trevidy/birthday-bot/all_frames.h

// Tổng hợp 772 frames - 128x64 pixels
// @khoi2mai
#ifndef ALL_FRAMES_H
#define ALL_FRAMES_H

#include "frames/frame_00000.h"
#include "frames/frame_00001.h"
#include "frames/frame_00002.h"
#include "frames/frame_00003.h"
#include "frames/frame_00004.h"
#include "frames/frame_00005.h"
#include "frames/frame_00006.h"
#include "frames/frame_00007.h"
#include "frames/frame_00008.h"
#include "frames/frame_00009.h"
#include "frames/frame_00010.h"
#include "frames/frame_00011.h"
#include "frames/frame_00012.h"
#include "frames/frame_00013.h"
#include "frames/frame_00014.h"
#include "frames/frame_00015.h"
#include "frames/frame_00016.h"
#include "frames/frame_00017.h"
#include "frames/frame_00018.h"
#include "frames/frame_00019.h"
#include "frames/frame_00020.h"
#include "frames/frame_00021.h"
#include "frames/frame_00022.h"
#include "frames/frame_00023.h"
#include "frames/frame_00024.h"
#include "frames/frame_00025.h"
#include "frames/frame_00026.h"
#include "frames/frame_00027.h"
#include "frames/frame_00028.h"
#include "frames/frame_00029.h"
#include "frames/frame_00030.h"
#include "frames/frame_00031.h"
#include "frames/frame_00032.h"
#include "frames/frame_00033.h"
#include "frames/frame_00034.h"
#include "frames/frame_00035.h"
#include "frames/frame_00036.h"
#include "frames/frame_00037.h"
#include "frames/frame_00038.h"
#include "frames/frame_00039.h"
#include "frames/frame_00040.h"
#include "frames/frame_00041.h"
#include "frames/frame_00042.h"
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
  frame_660, frame_661, frame_662, frame_663, frame_664, 
  frame_665, frame_666, frame_667, frame_668, frame_669, 
  frame_670, frame_671, frame_672, frame_673, frame_674, 
  frame_675, frame_676, frame_677, frame_678, frame_679, 
  frame_680, frame_681, frame_682, frame_683, frame_684, 
  frame_685, frame_686, frame_687, frame_688, frame_689, 
  frame_690, frame_691, frame_692, frame_693, frame_694, 
  frame_695, frame_696, frame_697, frame_698, frame_699, 
  frame_700, frame_701, frame_702, frame_703, frame_704, 
  frame_705, frame_706, frame_707, frame_708, frame_709, 
  frame_710, frame_711, frame_712, frame_713, frame_714, 
  frame_715, frame_716, frame_717, frame_718, frame_719, 
  frame_720, frame_721, frame_722, frame_723, frame_724, 
  frame_725, frame_726, frame_727, frame_728, frame_729, 
  frame_730, frame_731, frame_732, frame_733, frame_734, 
  frame_735, frame_736, frame_737, frame_738, frame_739, 
  frame_740, frame_741, frame_742, frame_743, frame_744, 
  frame_745, frame_746, frame_747, frame_748, frame_749, 
  frame_750, frame_751, frame_752, frame_753, frame_754, 
  frame_755, frame_756, frame_757, frame_758, frame_759, 
  frame_760, frame_761, frame_762, frame_763, frame_764, 
  frame_765, frame_766, frame_767, frame_768, frame_769, 
  frame_770, frame_771
};

#define TOTAL_FRAMES 772
#define FRAME_WIDTH 128
#define FRAME_HEIGHT 64

#endif // ALL_FRAMES_H
